FirstTestStation/InterconnectIO_Box/DOC/Image/box_panel.jpg

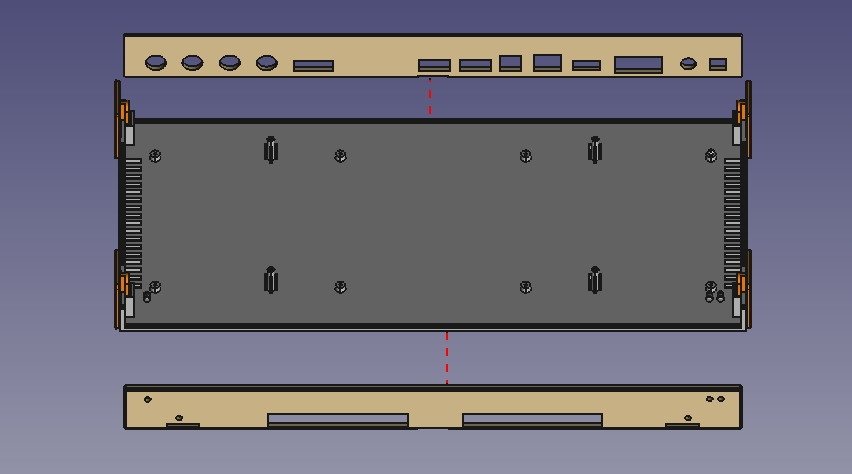
DOC/Image/box_panel.jpg
