FirstTestStation/InterconnectIO_Box/DOC/Image/Box_screw.jpg

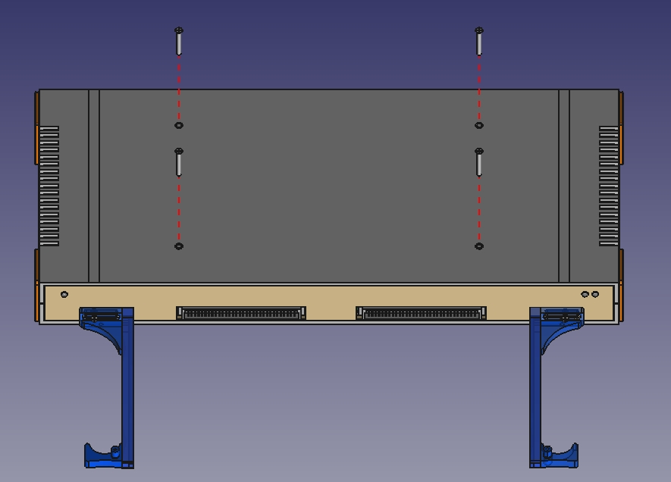
DOC/Image/Box_screw.jpg
