FirstTestStation/InterconnectIO_Box/DOC/Image/power.jpg

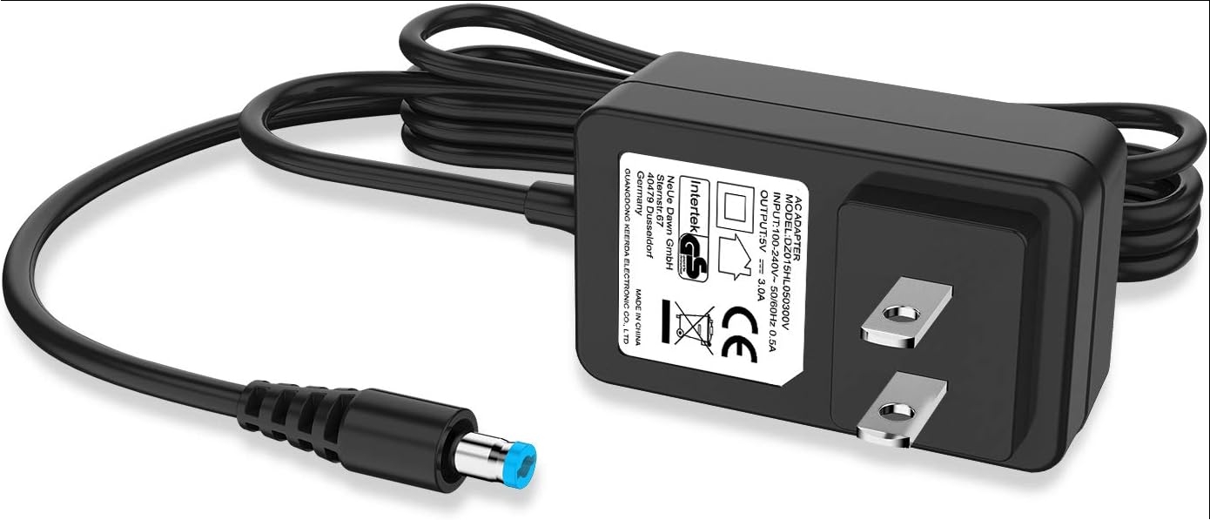
DOC/Image/power.jpg
