FirstTestStation/InterconnectIO_Box/DOC/Image/selftest.jpg

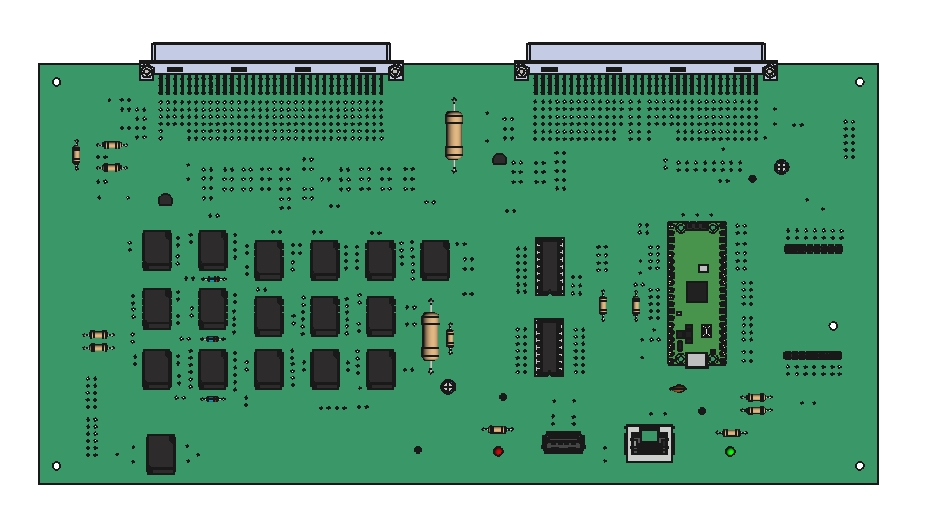
DOC/Image/selftest.jpg
